mizma/SlimDash/hardware-rev1/Assets/PCB2.jpg

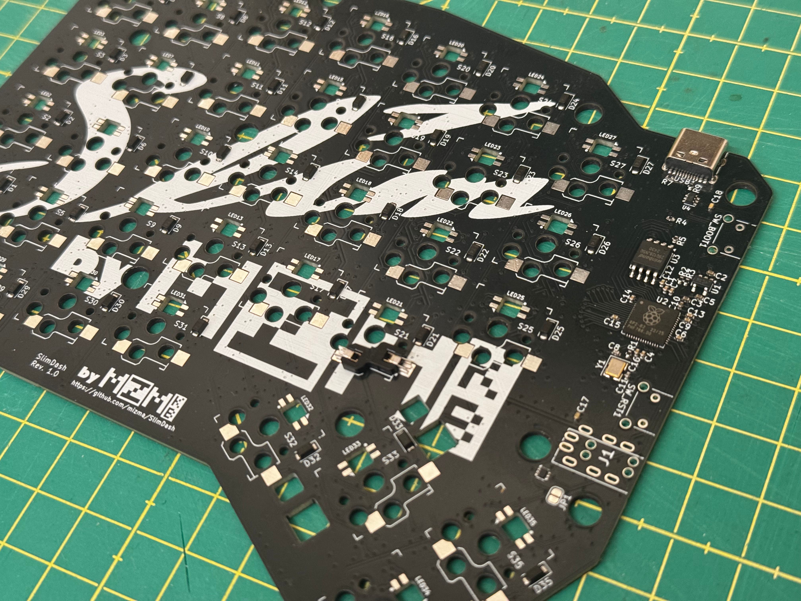
hardware-rev1/Assets/PCB2.jpg
