mizma/SlimDash/Assets/PartsPositioning.png

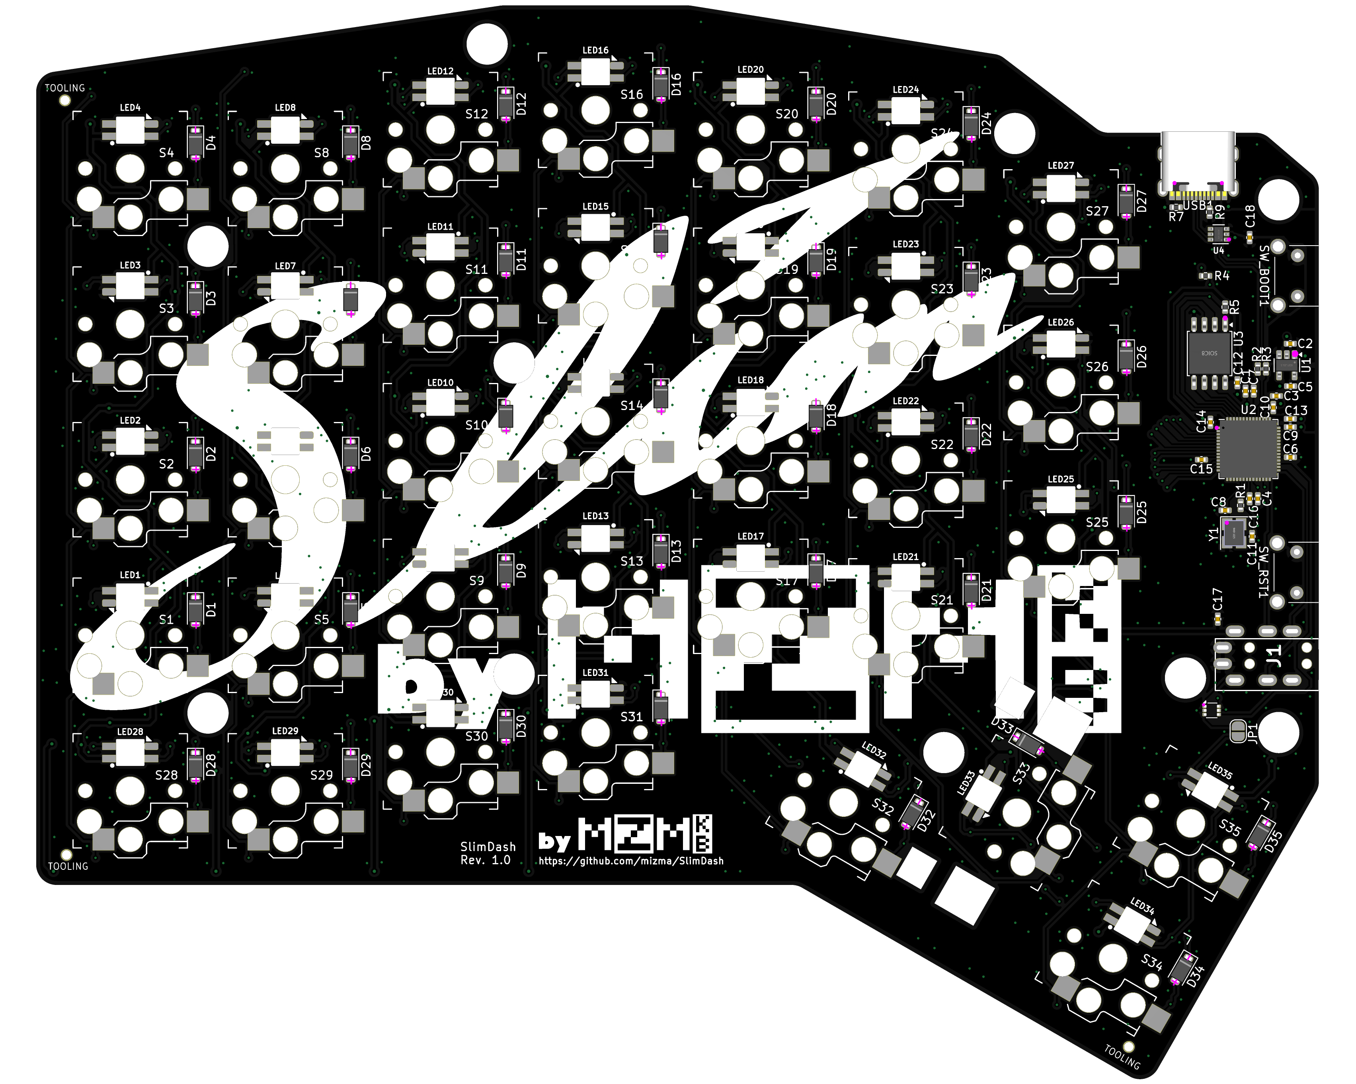
Assets/PartsPositioning.png
